FoZo/esp32-pc-control/kicad/esp32-pc-control/esp32-pc-control.kicad_pcb

## KiCad design Schematics/RCfilter/RCfilter.kicad_sch

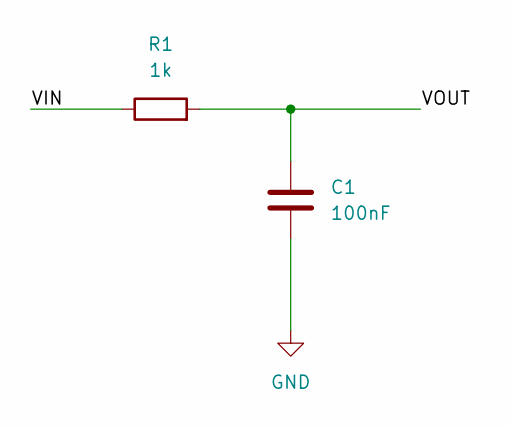
[picture p3: schematic RCfilter.kicad_sch]

Parts:
C1: 100nF
R1: 1k

Connections:
GND: C1.2
VIN: R1.1
VOUT: C1.1, R1.2
